nitishisskittish/Astrapad/KiCad (PCB)/3D Models/seeed-studio-xiao-rp2040-3d-model/Seeed Studio XIAO RP2040 v26/FusionAssetName[Active]/Images.BlobParts/Image.a9025d1d-726d-4056-92f7-61b905320149.jpg

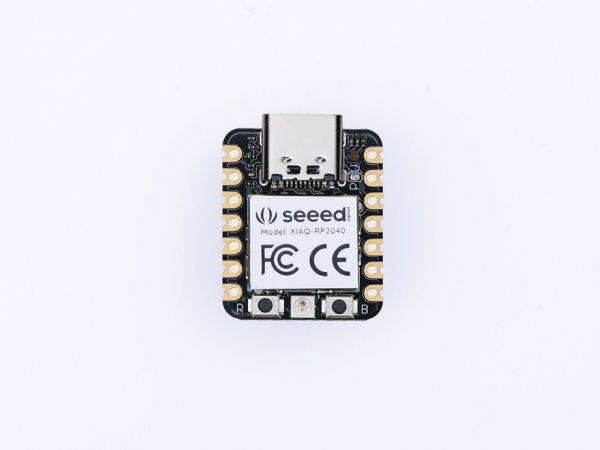
KiCad (PCB)/3D Models/seeed-studio-xiao-rp2040-3d-model/Seeed Studio XIAO RP2040 v26/FusionAssetName[Active]/Images.BlobParts/Image.a9025d1d-726d-4056-92f7-61b905320149.jpg
